MayaPosch/DebounceHat/debounce_hat_rev1_2_003a.jpg

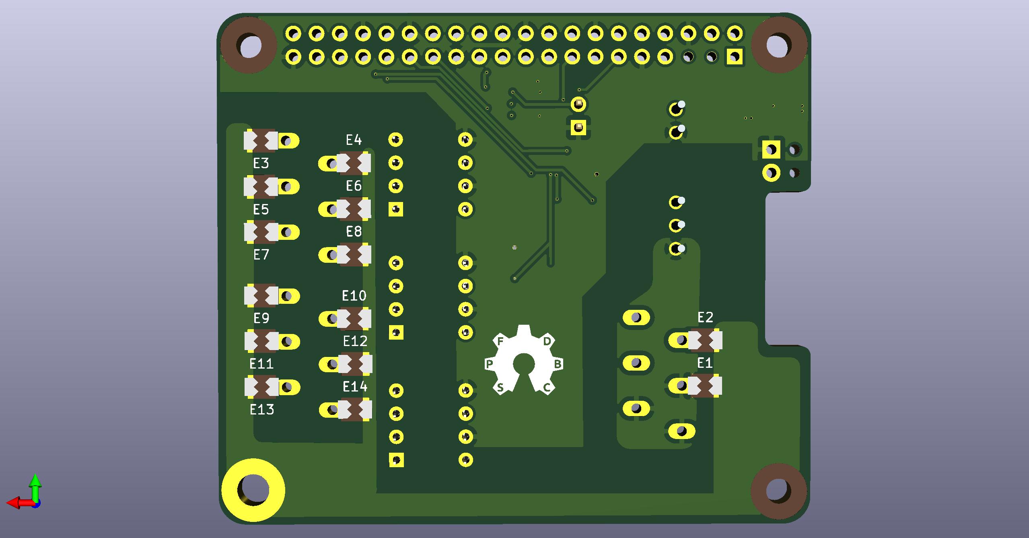
debounce_hat_rev1_2_003a.jpg
