MayaPosch/DebounceHat/debounce_hat_rev1_2_005a.jpg

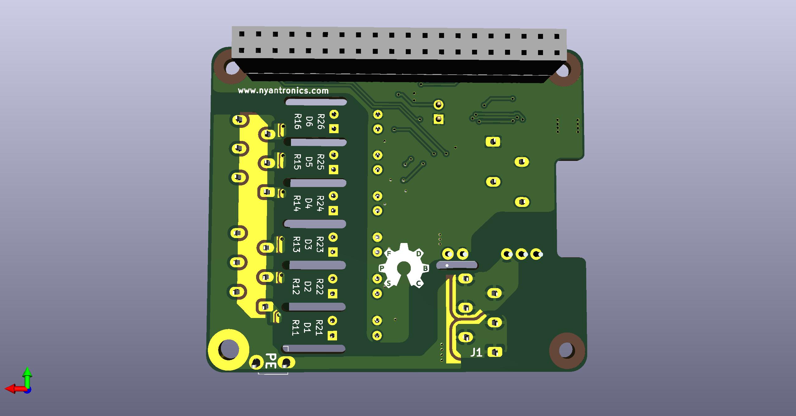
debounce_hat_rev1_2_005a.jpg
