MayaPosch/DebounceHat/debounce_shield.bak2.jpg

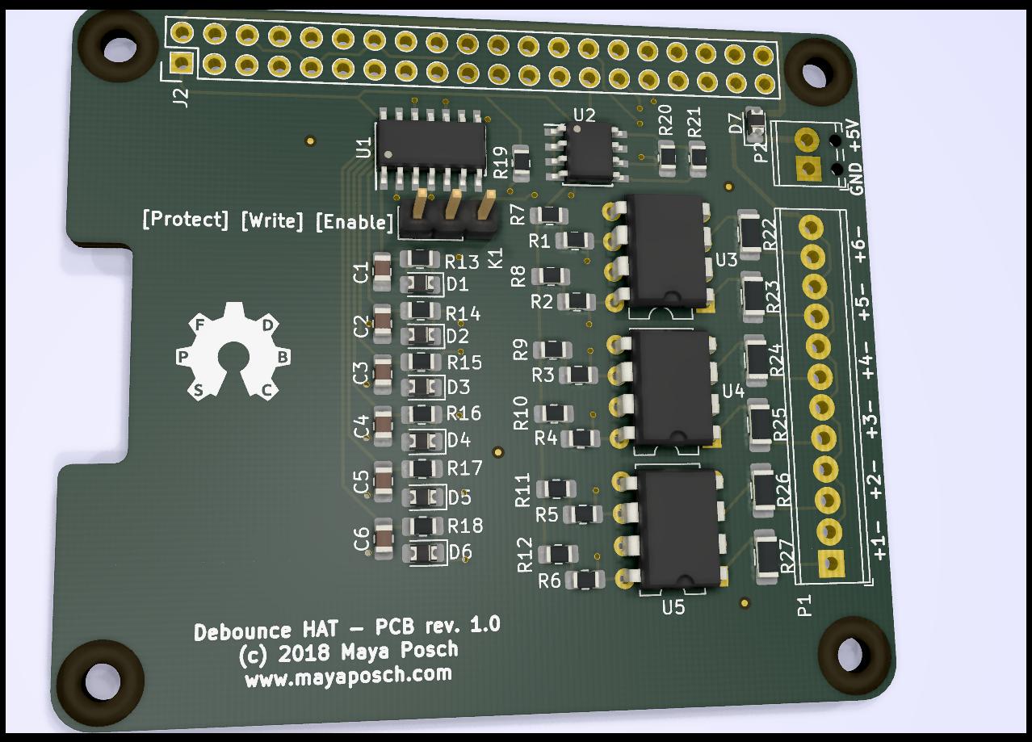
debounce_shield.bak2.jpg
