MayaPosch/DebounceHat/debounce_shield.bak.jpg

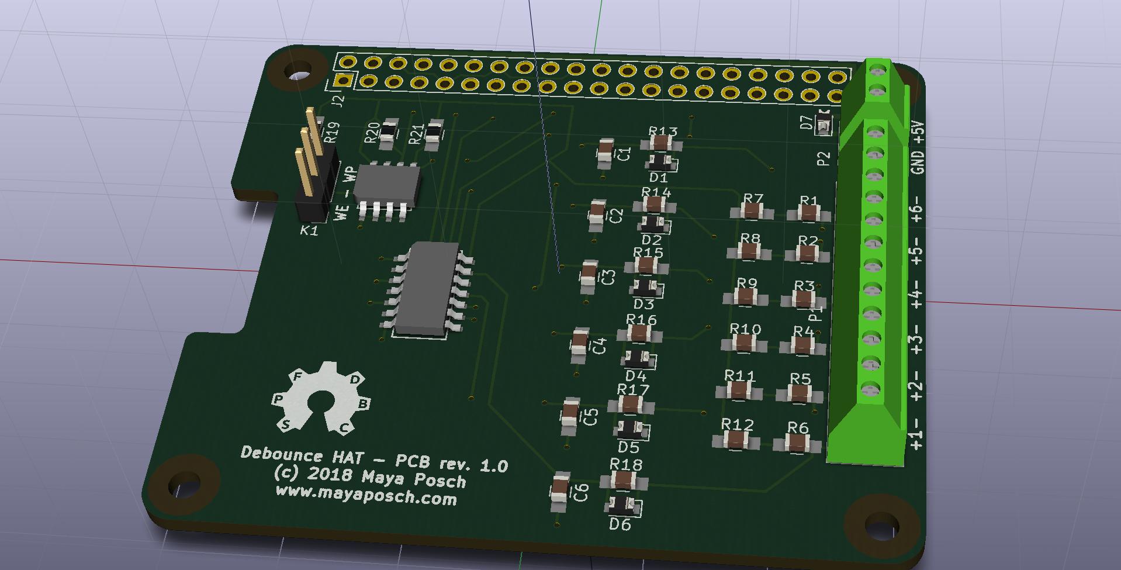
debounce_shield.bak.jpg
