MayaPosch/DebounceHat/debounce_shield_rev1_2_001.jpg

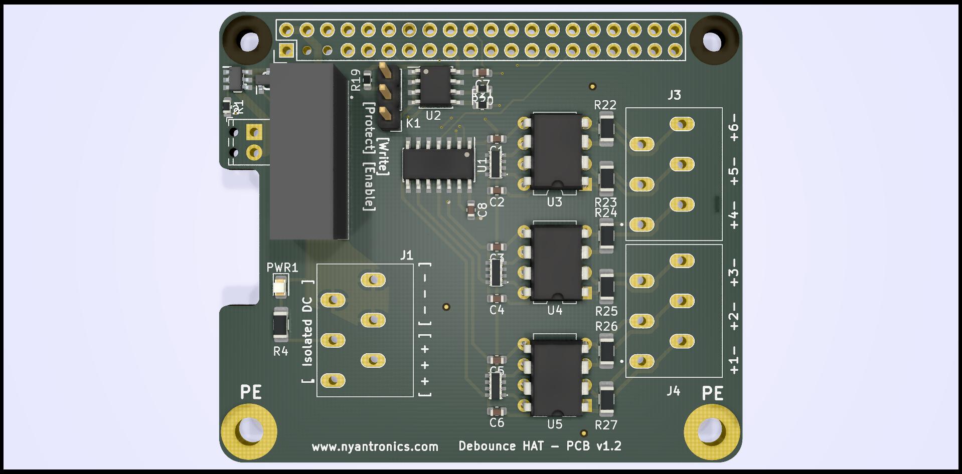
debounce_shield_rev1_2_001.jpg
