MayaPosch/DebounceHat/debounce_shield_rev1_2_002a.jpg

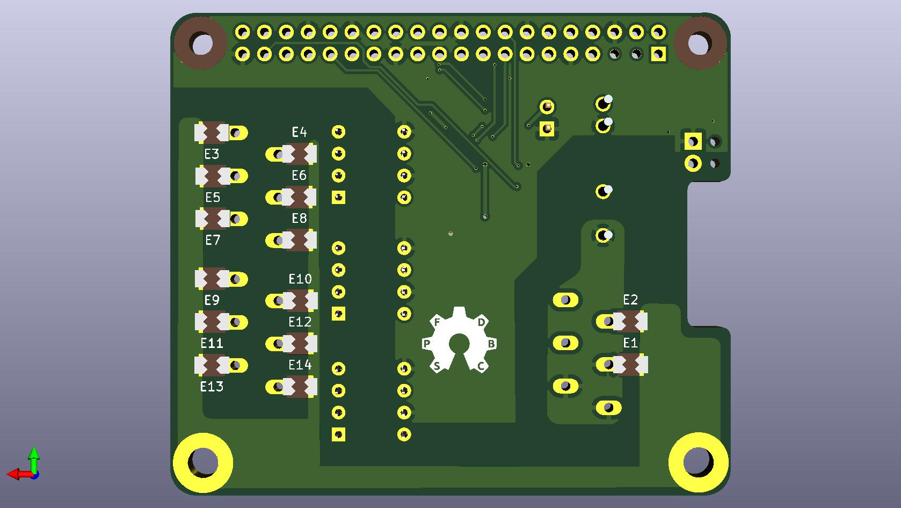
debounce_shield_rev1_2_002a.jpg
