MayaPosch/DebounceHat/debounce_shield_rev1_2_003.jpg

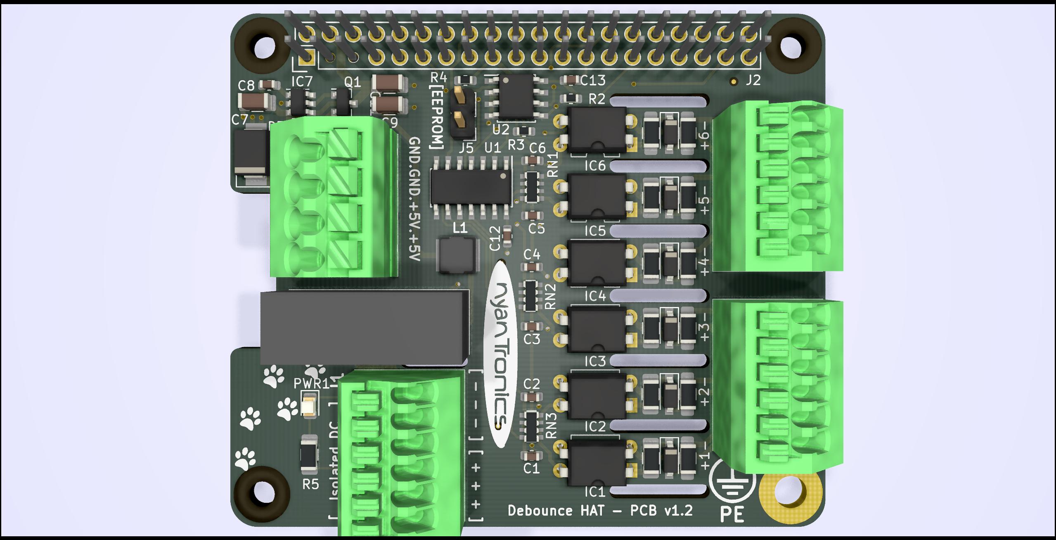
debounce_shield_rev1_2_003.jpg
