MayaPosch/DebounceHat/debounce_shield_rev1_2_004.jpg

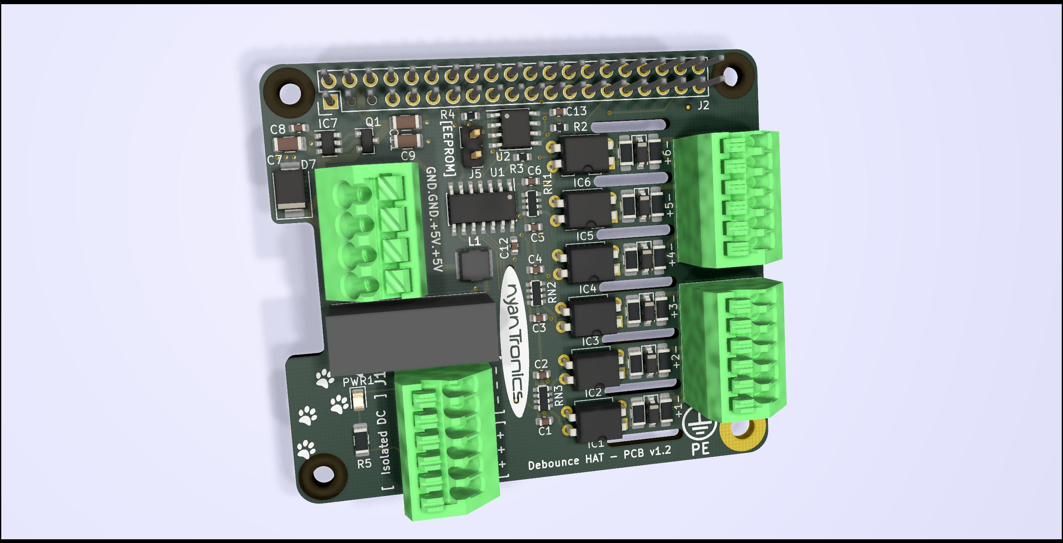
debounce_shield_rev1_2_004.jpg
